go4retro/MIDIMaestro/pcb/MIDIMaestro v1 PCB.png

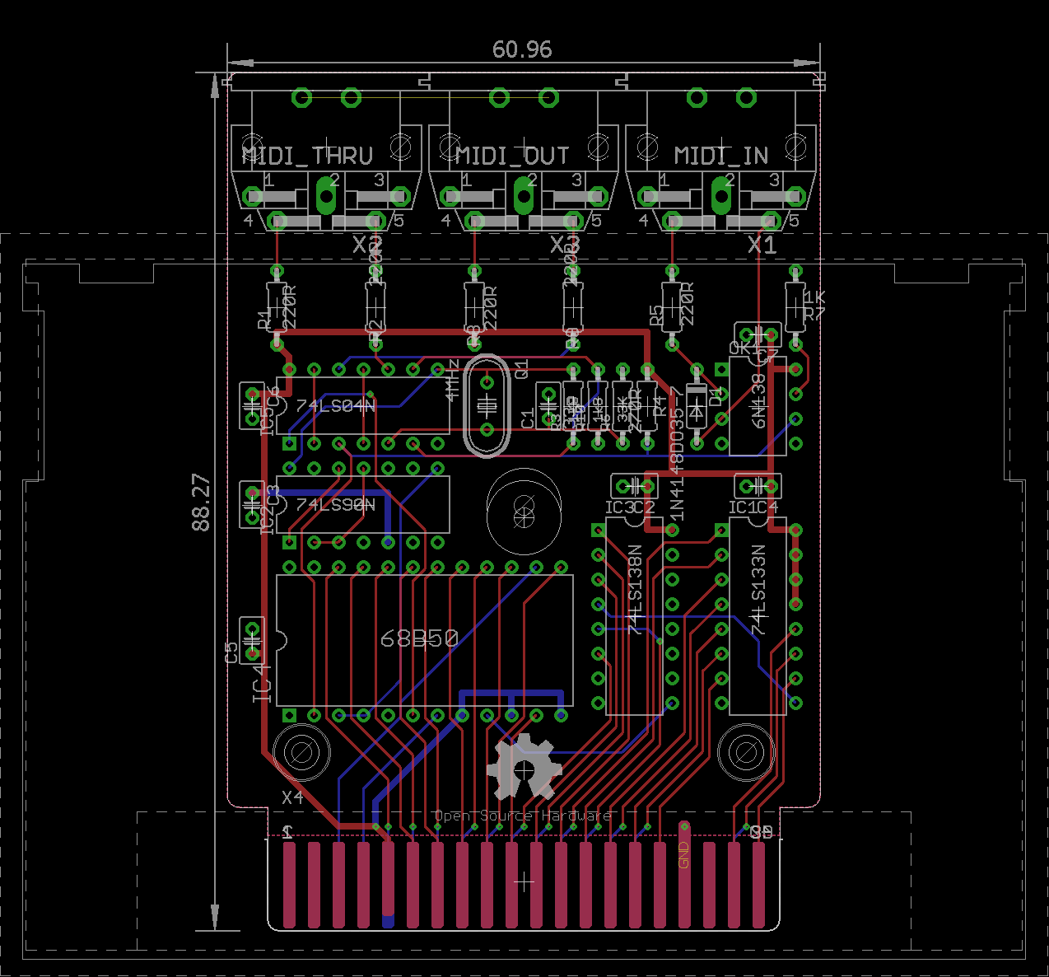
pcb/MIDIMaestro v1 PCB.png
