go4retro/MIDIMaestro/pcb/MIDIMaestro v3d Schematic.png

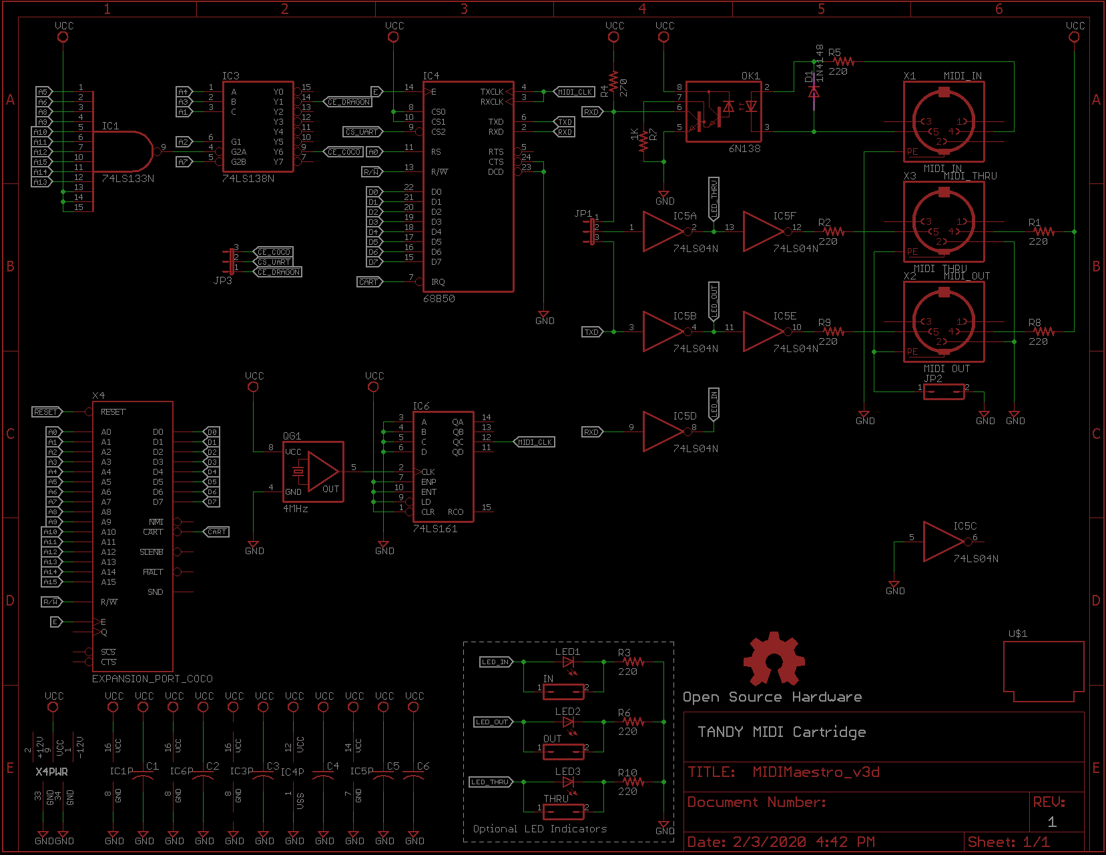
pcb/MIDIMaestro v3d Schematic.png
