go4retro/MIDIMaestro/ref/DSCN0305.JPG

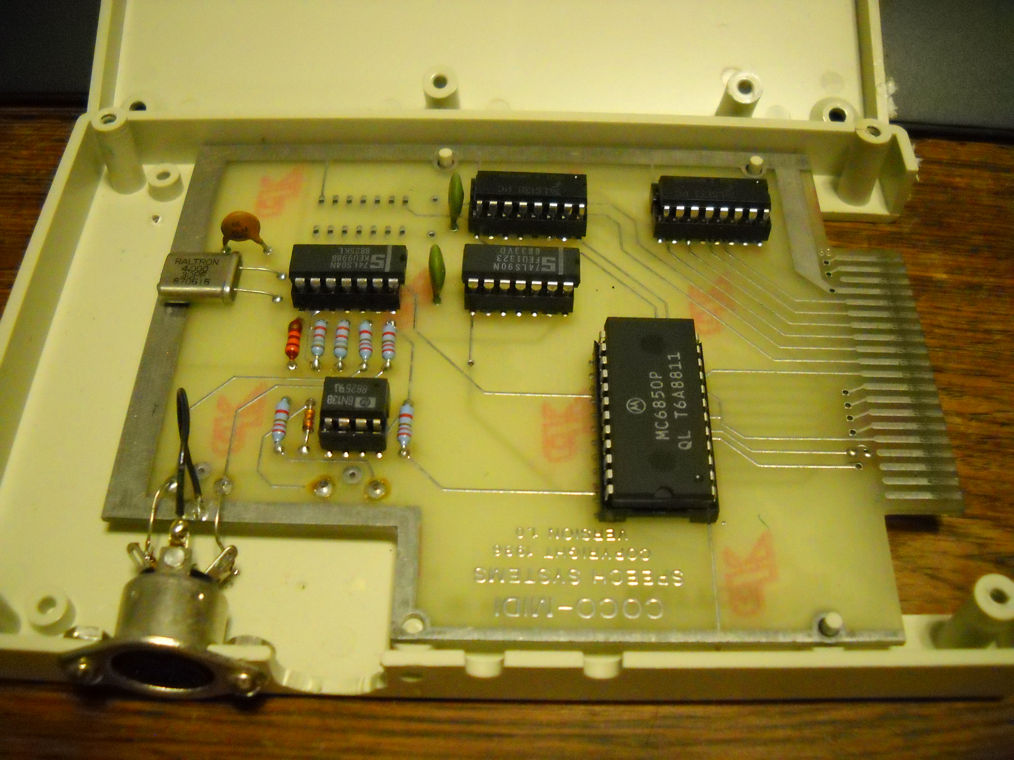
ref/DSCN0305.JPG
