go4retro/MIDIMaestro/ref/EMM_85_04_powertran_bb_5.jpg

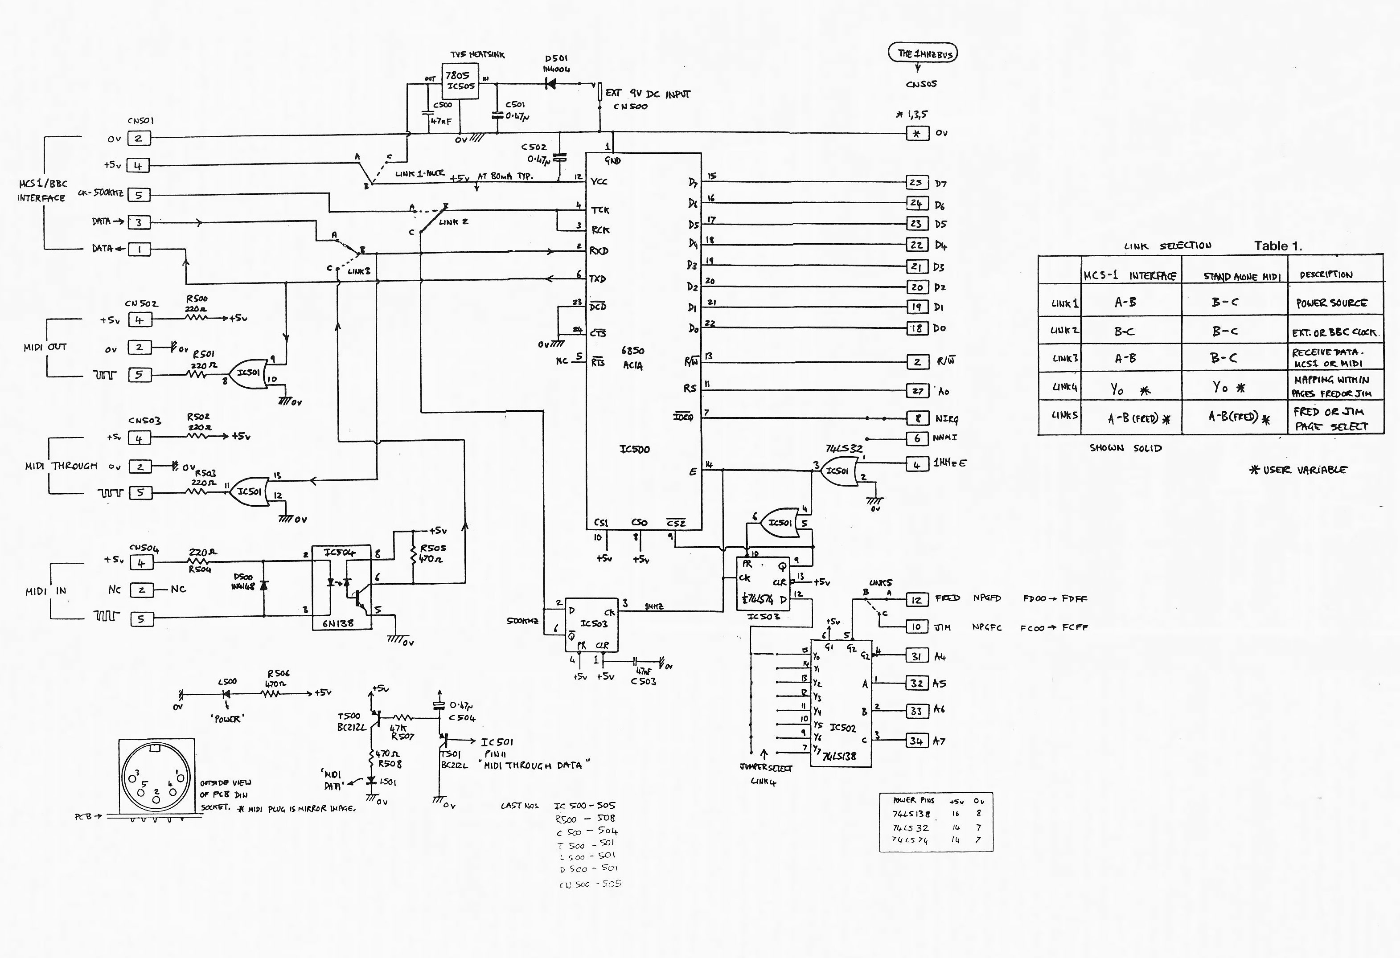
ref/EMM_85_04_powertran_bb_5.jpg
